luxus0946/Signal-Generator-based-on-DDS/HDK/3D仿真图/3D_反面(含CH340).png

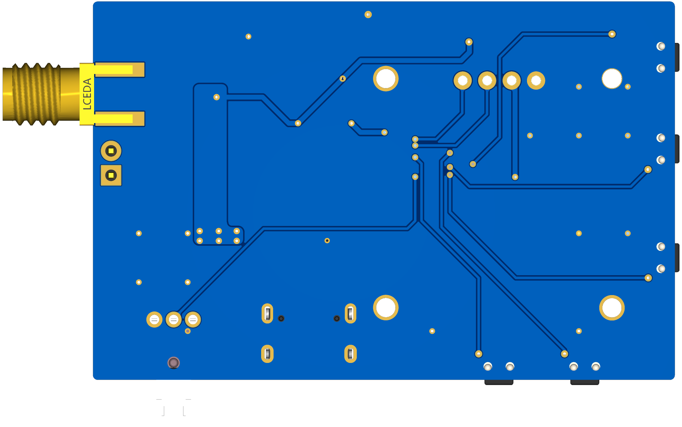
HDK/3D仿真图/3D_反面(含CH340).png
