luxus0946/Signal-Generator-based-on-DDS/HDK/3D仿真图/3D_反面(无CH340).png

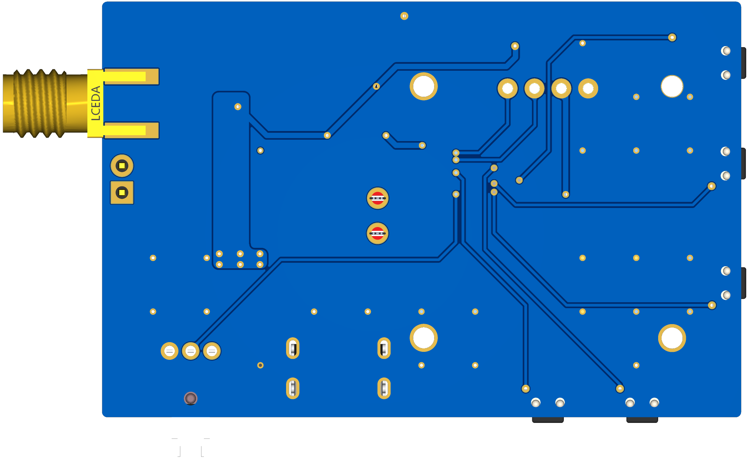
HDK/3D仿真图/3D_反面(无CH340).png
