luxus0946/Signal-Generator-based-on-DDS/HDK/3D仿真图/3D_外壳侧面.png

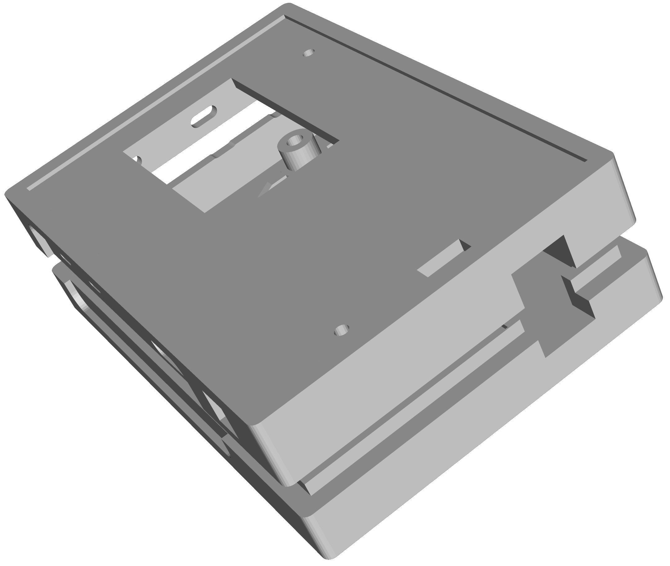
HDK/3D仿真图/3D_外壳侧面.png
