luxus0946/Signal-Generator-based-on-DDS/HDK/PCB/PCB(CH340).png

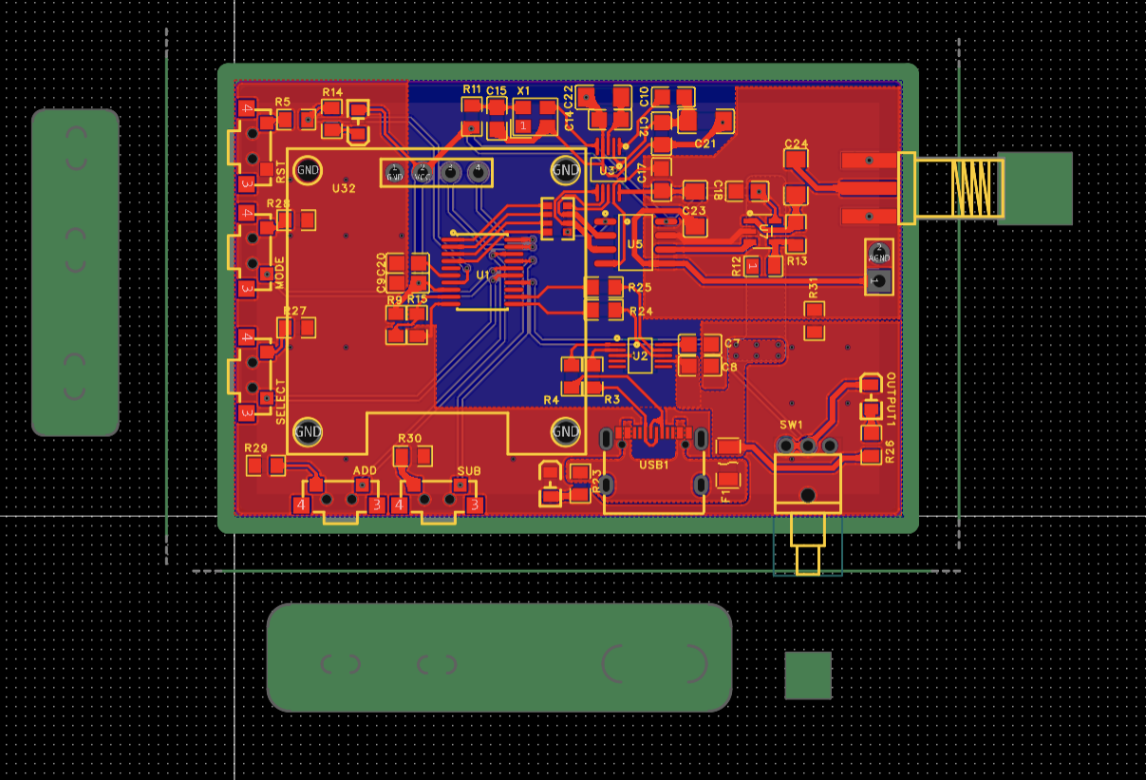
HDK/PCB/PCB(CH340).png
