luxus0946/Signal-Generator-based-on-DDS/HDK/PCB/PCB(无CH340).png

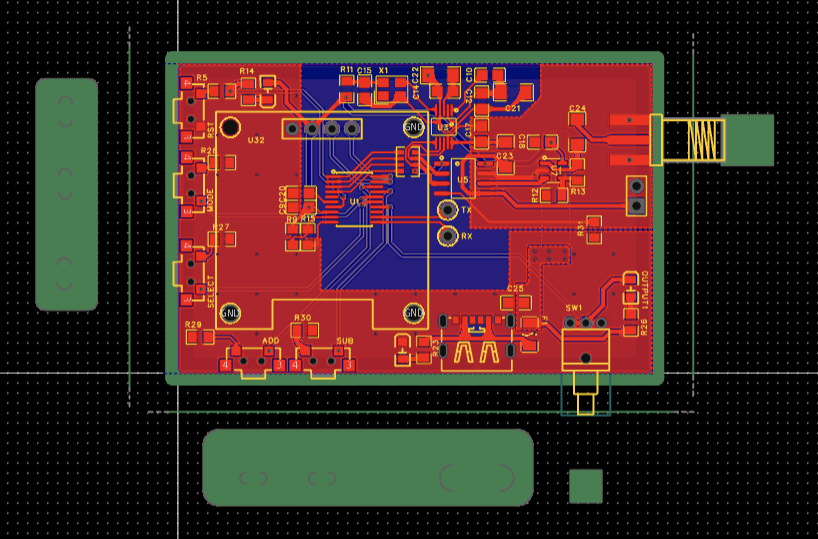
HDK/PCB/PCB(无CH340).png
