luxus0946/Signal-Generator-based-on-DDS/HDK/原理图/based-on-dds(含有CH340)/SCH_DDS_1-MIAN_2024-01-11.png

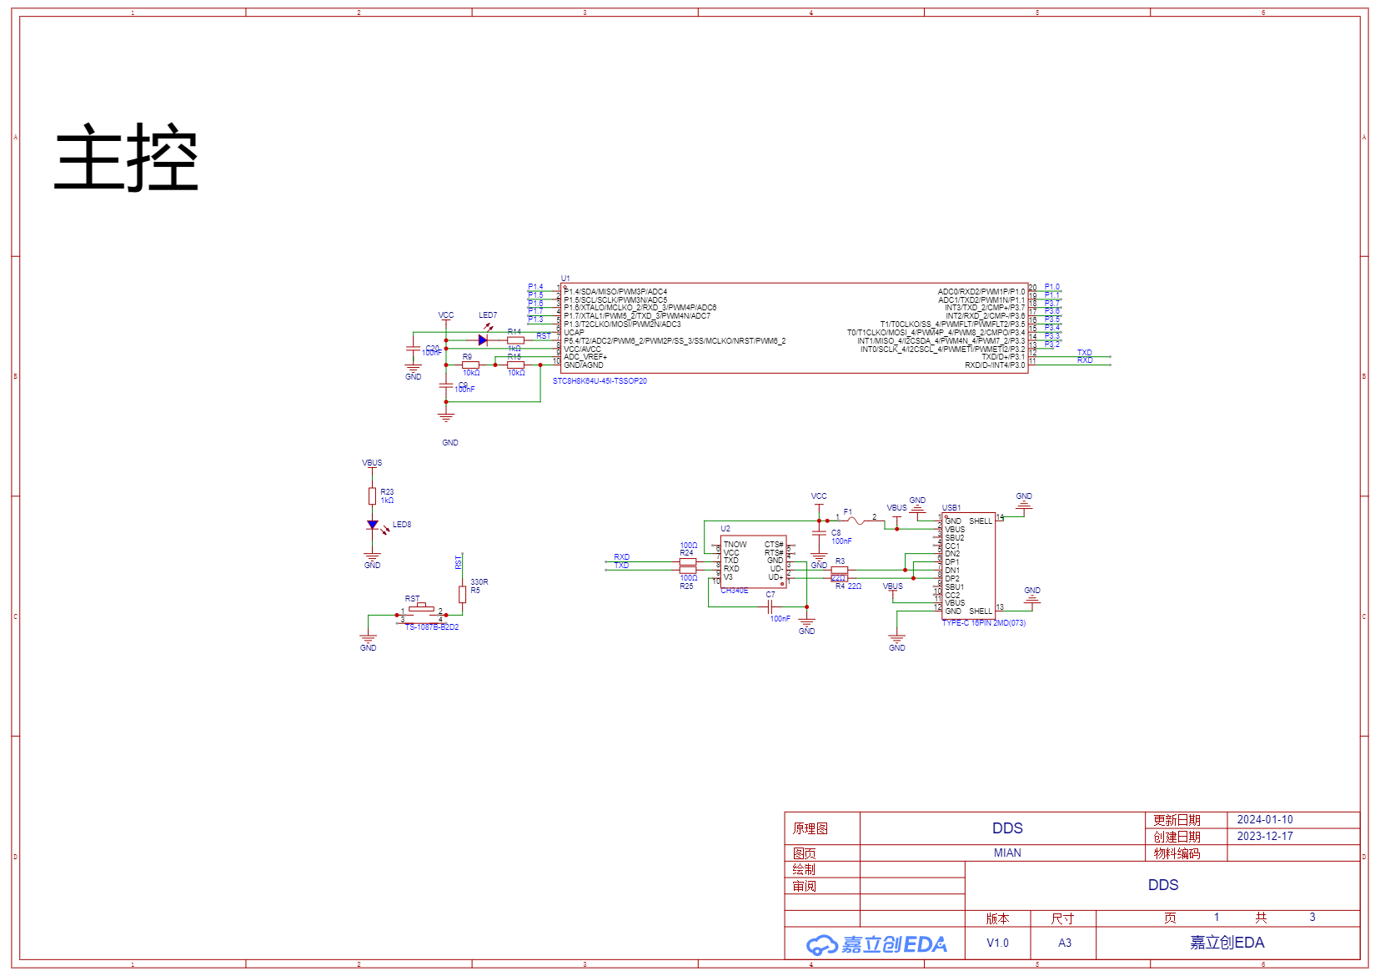
HDK/原理图/based-on-dds(含有CH340)/SCH_DDS_1-MIAN_2024-01-11.png
