luxus0946/Signal-Generator-based-on-DDS/HDK/原理图/based-on-dds(含有CH340)/SCH_DDS_2-AD9833_2024-01-11.png

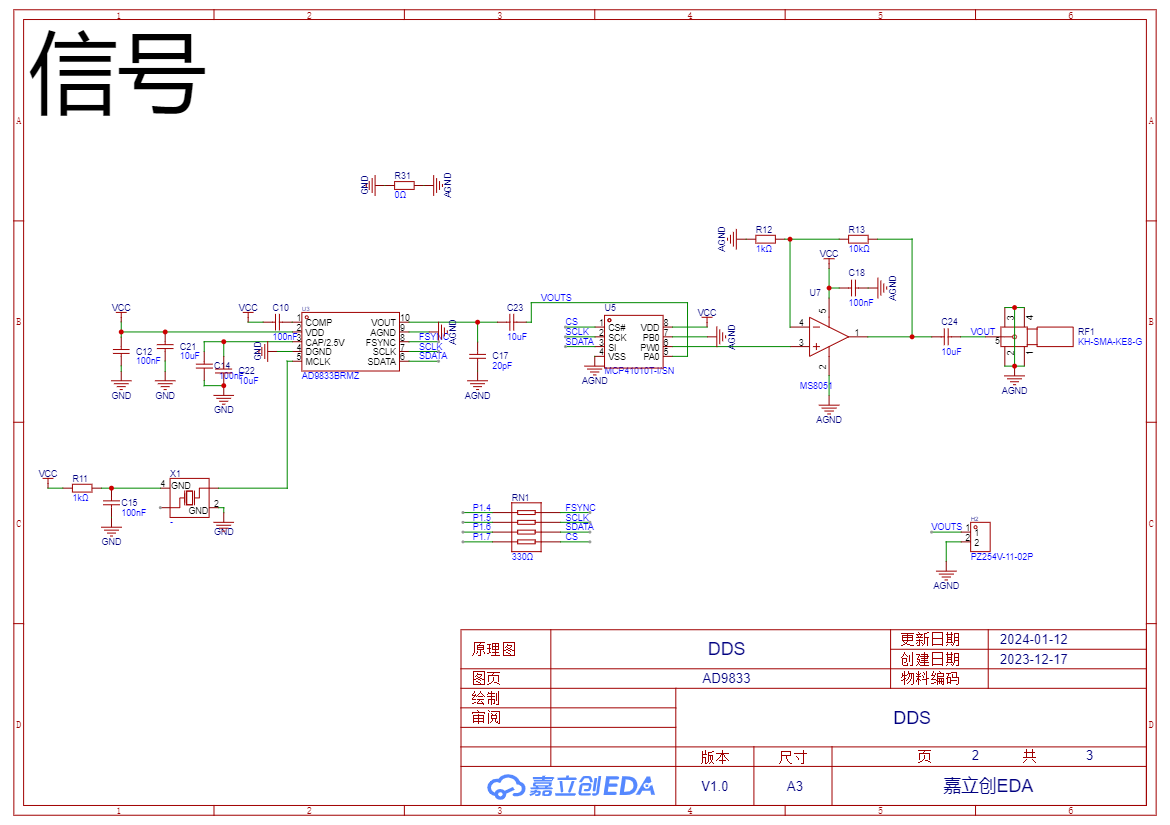
HDK/原理图/based-on-dds(含有CH340)/SCH_DDS_2-AD9833_2024-01-11.png
